Wackadoos/instruments/circuitry/instruments.kicad_pcb

## KiCad design Hardware/Controller/Controller.kicad_sch

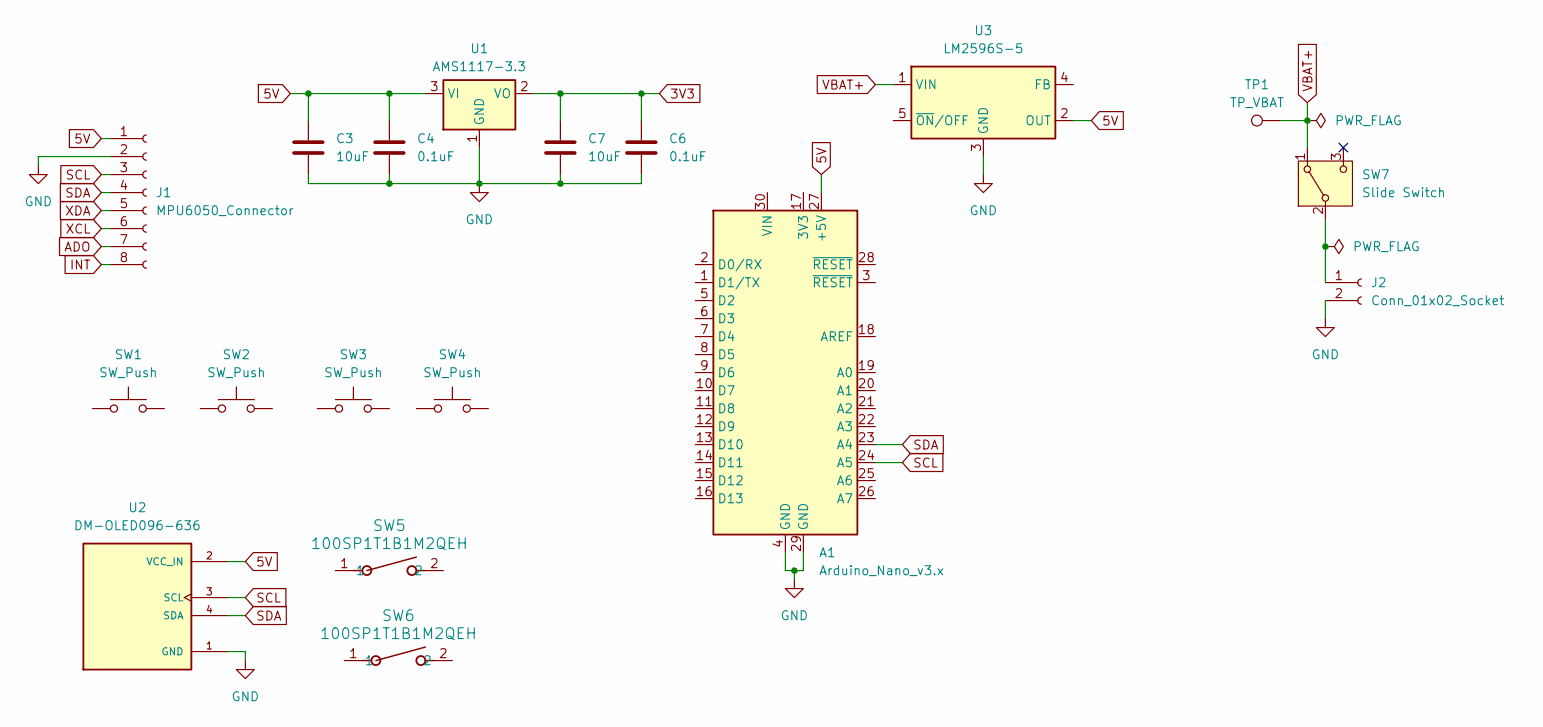
[picture p7: schematic Controller.kicad_sch]

Parts:
A1: Arduino_Nano_v3.x; Arduino_Nano
C3, C7: 10uF; C_0805_2012Metric
C4, C6: 0.1uF; C_0603_1608Metric
J1: MPU6050_Connector
J2: Conn_01x02_Socket
SW1, SW2, SW3, SW4: SW_Push
SW5, SW6: 100SP1T1B1M2QEH; SW_100SP1T_12P7X6P86_EWI
SW7: Slide Switch; SW_Slide-03_Wuerth-WS-SLTV_10x2.5x6.4_P2.54mm
TP1: TP_VBAT; TestPoint_Pad_2.0x2.0mm
U1: AMS1117-3.3; SOT-223-3_TabPin2
U2: DM-OLED096-636; MODULE_DM-OLED096-636; PARTREV 2018-09-10
U3: LM2596S-5; TO-263-5_TabPin3

Connections:
3V3: C6.1, C7.1, U1.2 (VO)
5V: A1.27 (+5V), C3.1, C4.1, J1.1, U1.3 (VI), U2.2 (VCC_IN), U3.2 (OUT)
ADO: J1.7
GND: A1.4 (GND), A1.29 (GND), C3.2, C4.2, C6.2, C7.2, J1.2, J2.2, U1.1 (GND), U2.1 (GND), U3.3 (GND)
INT: J1.8
unnamed: J2.1, SW7.2 (B)
SCL: A1.24 (A5), J1.3, U2.3 (SCL)
SDA: A1.23 (A4), J1.4, U2.4 (SDA)
VBAT+: SW7.1 (A), TP1.1, U3.1 (VIN)
XCL: J1.6
XDA: J1.5
