Wackadoos/instruments/src/modules/temps.cpp

#include "temps.h"

#include "state.h"
#include "utils/errors.h"
#include "utils/logging.h"

IntervalMetric TEMPS::dataRequestTime = IntervalMetric();
IntervalMetric TEMPS::dataAcquisitionTime = IntervalMetric();
IntervalMetric TEMPS::dataProcessTime = IntervalMetric();
DallasTemperature TEMPS::sensors = DallasTemperature();

void TEMPS::init(OneWire* oneWire) {
  sensors.setOneWire(oneWire);
  sensors.begin();
  auto numberOfDevices = sensors.getDeviceCount();

  if (numberOfDevices == 0) {
    Errors::logError(Error::NO_TEMPS_FOUND);
    return;
  }
  if (numberOfDevices != EXPECTED_SENSOR_COUNT) {
    Errors::logError(Error::INCORRECT_NUM_TEMPS);
    return;
  }

  for (int i = 0; i < EXPECTED_SENSOR_COUNT; i++) {
    if (sensors.getAddress(addresses[i], i)) {
      sensors.setResolution(addresses[i], SENSOR_RESOLUTION);
      if (sensors.getResolution(addresses[i]) != SENSOR_RESOLUTION) {
        Errors::logError(Error::TEMP_RESOLUTION_INCORRECT);  // Not a reason to disable the module, just to notify
      }
      sensors.setWaitForConversion(false);  // Enable async mode
    } else {
      Errors::logError(Error::GHOST_TEMP_PROBE);
      return;
    }
  }

  if (!sortAddresses(addresses, EXPECTED_SENSOR_COUNT)) {
    Errors::logError(Error::DUPLICATE_TEMP_SENSOR_IDS);
    return;
  }

  dataRequestTime.init(F("Temp Req"), F("Time to send Temperature Request"));
  dataAcquisitionTime.init(F("Temp Acq"), F("Time until Temperature Response"));
  dataProcessTime.init(F("Temp Proc"), F("Time to process Temperature Data"));
  enabled = true;
}

void TEMPS::update() {
  if (enabled) {
    dataRequestTime.start();
    sensors.requestTemperaturesByAddress(addresses[current_address]);
    newData = true;
    dataRequestTime.stop();
    dataAcquisitionTime.start();
  }
}

void TEMPS::run() {
  if (enabled && newData && sensors.isConversionComplete()) {  // isConversionComplete reads i2c bit which has micros waits. Could check this less often for efficiency!
    dataAcquisitionTime.stop();
    dataProcessTime.start();
    newData = false;
    float tempC = sensors.getTempC(addresses[current_address]);

    if (tempC == DEVICE_DISCONNECTED_C) {
      Errors::logError(Error::TEMP_UNREADABLE);
    } else {
      if (current_address == 0) {
        State::temp_motor_1 = tempC;
        Logging::logDebug(F("Temp Probe 1: "), tempC);
      } else if (current_address == 1) {
        State::temp_motor_2 = tempC;
        Logging::logDebug(F("Temp Probe 2: "), tempC);
      }
    }

    current_address++;
    if (current_address >= EXPECTED_SENSOR_COUNT) {
      current_address = 0;
    }
    dataProcessTime.stop();
  }
}

int8_t TEMPS::compare(DeviceAddress a, DeviceAddress b) {
  for (uint8_t i = 0; i < sizeof(DeviceAddress); i++) {
    if (a[i] > b[i]) return 1;
    if (a[i] < b[i]) return -1;
  }
  return 0;
}

bool TEMPS::sortAddresses(DeviceAddress* addresses, uint8_t count) {  // Insertion Sort
  for (uint8_t i = 1; i < count; i++) {
    uint8_t key[sizeof(DeviceAddress)];
    for (uint8_t k = 0; k < sizeof(DeviceAddress); k++) key[k] = addresses[i][k];

    int8_t j = i - 1;
    while (j >= 0) {
      int8_t cmp = compare(addresses[j], key);
      if (cmp <= 0) break;
      for (uint8_t k = 0; k < sizeof(DeviceAddress); k++) addresses[j + 1][k] = addresses[j][k];
      j--;
    }
    for (uint8_t k = 0; k < sizeof(DeviceAddress); k++) addresses[j + 1][k] = key[k];
  }

  for (uint8_t i = 0; i + 1 < count; i++) {
    uint8_t same = 1;
    for (uint8_t k = 0; k < sizeof(DeviceAddress); k++) {
      if (addresses[i][k] != addresses[i + 1][k]) {
        same = 0;
        break;
      }
    }
    if (same) return false;
  }

  return true;
}
