Wackadoos/instruments/src/modules/GPS.h

#pragma once

#include <Arduino.h>
#include <NMEAGPS.h>

#include "utils/metrics.h"

#ifndef NMEAGPS_INTERRUPT_PROCESSING
#error You must define NMEAGPS_INTERRUPT_PROCESSING in NMEAGPS_cfg.h!
#endif

class GPS {
 public:
  static void init();
  static void run();
  static inline bool isEnabled() { return enabled; };

  static gps_fix fix;
  inline static bool dateTimeCalibrated = false;

 private:
  static NMEAGPS gps;
  static IntervalMetric dataProcessTime;

  inline static bool enabled = false;
  inline static bool setSubSecond = false;

  static void GPSisr(uint8_t c);
  static void PPSisr();
};
