Wackadoos/instruments/src/modules/eeprom.h

#pragma once

#include <Arduino.h>
#include <SparkFun_External_EEPROM.h>
#include <Wire.h>

class EEPROM {
 public:
  static ExternalEEPROM eeprom;

  static void init(TwoWire* wire);
  static inline bool isEnabled() { return enabled; };

 private:
  inline static bool enabled = false;
};
