Wackadoos/instruments/demo/VESC.cpp

//! FLIPSKY 75100 ESC Communications
#include <Arduino.h>
#include <VescUart.h>

VescUart VESC = VescUart(10);

void setup() {
  Serial.begin(500000);
  while (!Serial)
    delay(100);  // wait for native usb
  delay(3000);
  Serial.println(F("ESC test"));

  //! NOTE apparently 115200 baud on vesc to arduino isn't reliable (due to clock), use 250000. (see timings table for 16mhz clock https://wormfood.net/avrbaudcalc.php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)
  Serial2.begin(250000);

  VESC.setDebugPort(&Serial);
  VESC.setSerialPort(&Serial2);
}

void loop() {
  if (VESC.getVescValues()) {
    // Serial.println(VESC.data.rpm);
    // Serial.println(VESC.data.inpVoltage);
    // Serial.println(VESC.data.ampHours);
    // Serial.println(VESC.data.tachometerAbs);
    VESC.printVescValues();
  } else {
    Serial.println("Failed to get data!");
  }

  delay(500);
}
