Wackadoos/instruments/src/utils/errors.h

#pragma once

#include <Arduino.h>

#define CACHED_ERRORS 10

enum class Error : uint8_t {
  UNKNOWN,
  BMP280_UNINITIALISED,
  ATH20_UNINITIALISED,
  RTC_UNINITIALISED,
  RTC_LOST_POWER,
  RTC_OUT_OF_SYNC,
  IMU_UNINITIALISED,
  IMU_SAMPLE_RATE_ERR,
  IMU_INTERRUPT_ERR,
  IMU_DATA_READ_FAILED,
  NVRAM_UNINITIALISED,
  I2C_TIMEOUT,
  EEPROM_UNINITIALISED,
  SETTINGS_VERSION_CHANGED,
  SETTINGS_CHECKSUM_FAILED,
  SETTINGS_VOLATILE,
  NO_TEMPS_FOUND,
  INCORRECT_NUM_TEMPS,
  GHOST_TEMP_PROBE,
  TEMP_RESOLUTION_INCORRECT,
  DUPLICATE_TEMP_SENSOR_IDS,
  TEMP_UNREADABLE,
  VESC_DATA_UNAVAILABLE,
  VESC_REPORTED_UNCOMMON_ERROR,
  VESC_REPORTED_HARDWARE_FAULT,
  VESC_REPORTED_TEMPERATURE_FAULT,
  VESC_REPORTED_VOLTAGE_FAULT,
  VESC_REPORTED_FLASH_CORRUPTION,
  DISPLAY_UNINITIALISED,
  TOUCHSCREEN_UNINITIALISED,
  GPS_OVERRUN,
  SD_UNINITIALISED,
  SD_OPEN_FAILED,
  SD_PREALLOCATE_FAILED,
  SD_WRITE_FAILED,
  SD_LOG_OVERRUN,
  SD_STALLED
};

struct ErrorEvent {
  Error type;
  unsigned long seconds_epoch_time;  // Time of the FIRST occurrence
  uint32_t count;                    // Occurrences since first (1 = first)
};

class Errors {
 public:
  inline static ErrorEvent errors[CACHED_ERRORS] = {};  // Circular buffer of unique errors (each with an occurrence count) for display
  static void init();
  static void logError(Error error);
  static const __FlashStringHelper* errorDescription(Error error);
  static ErrorEvent newestError(uint8_t index);  // Newest-first, skipping UNKNOWN; {UNKNOWN, 0} past the end

 private:
  inline static uint8_t errors_head = 0;
  static void flushToLogfile(const ErrorEvent& errorEvent);
};
